f-io/dspCore/documentation/measurements/1vrms_dspCore(diff)_thd+n.jpeg

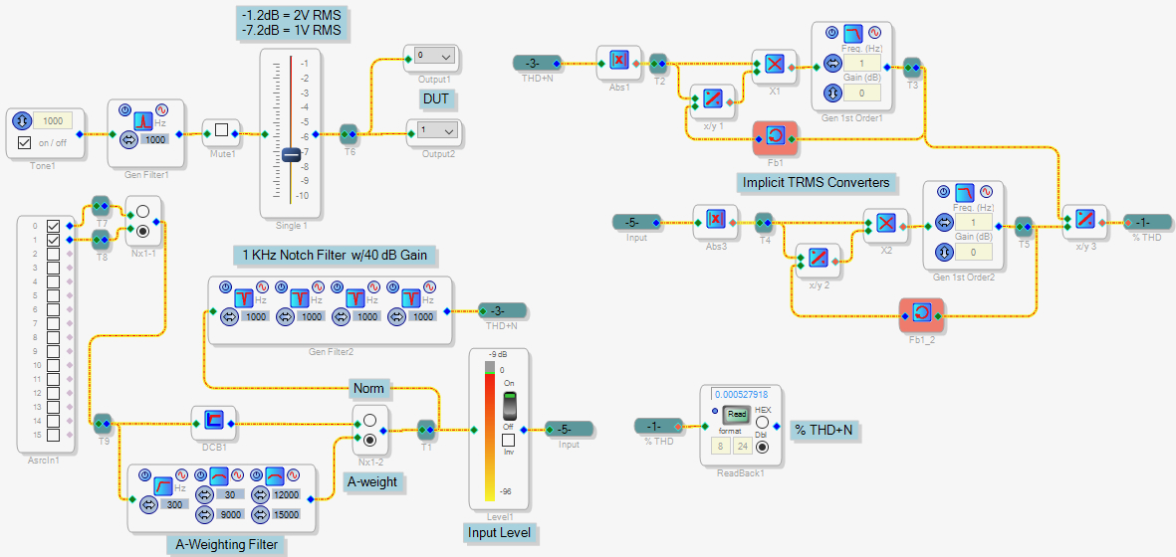
documentation/measurements/1vrms_dspCore(diff)_thd+n.jpeg
